iiko38/sleeperplan/published/first-model-2400x1400-options/3-courses/workshop.pdf

Sleeperplan | 9d70b40ac2ba | DRAFT_MARK_OUT_ONLY | 1

# SLEEPERPLAN / WORKSHOP PACK

### DRAFT_MARK_OUT_ONLY

## First rectangular bed draft - 2400 x 1400

As of 2026-09-06 | Generator 0.4.0 | Plan 9d70b40ac2ba3151
Worked example unless your own surveyed job file has been used. A reviewed status records human checks; it is not structural certification.
BED | OUTSIDE L x W x H (mm) | COURSES | CLEAR OPENING (mm) | FILL (litres)
first-bed-01 | 2400 x 1400 x 600 | 3 | 2200 x 1200 | 1452.0

### 12 labelled pieces | 56 fixing entries | 12 purchased sleepers | 6 saw cuts

Timber + screw purchases: GBP 354.60
Known subtotal: GBP 354.60. NOT a completed job cost. Unpriced items remain.
Cutting: exact. All explored cutting patterns and inventory states solved.
Use BUILD.md for the assembly sequence. Use cuts.csv for saw bands and fixings.csv for full coordinates. Treat all pilot entries marked UNCONFIRMED as mark-out only, not a drilling instruction.

# REVIEW GATES & ASSUMPTIONS

TYPE | CHECK
BLOCKER | Measure actual stock length/section, usable ends and saw kerf; update inputs before cutting.
BLOCKER | Review foundations, drainage, soil loads, support/bracing and any buried services on site.
BLOCKER | Review screw suitability, end-grain connections, penetration and spacing with a competent builder / supplier.
BLOCKER | Record reviewer, reviewed_on and review notes before releasing a workshop pack.
BLOCKER | Release readiness requires review.approved_physical_design_hash to equal the current physical design hash, so an edited job cannot inherit an old review. Run a draft plan, then copy the printed physical design hash into the job's review block after a genuine physical review.
NOTE | Screw heads, bearing seats, recesses and driver access are NOT modelled. On stacked courses a protruding head can stop the next course sitting flat even though all shafts pass the collision check, and recessing a seat deepens the hole and moves the tip. Confirm the head-seat detail with the actual hardware before stacking any course.
BLOCKER | wickes-287686: fixing centres are mark-out only. Confirm pilot diameter/depth or a manufacturer-supported no-pilot instruction; none is inferred.
BLOCKER | wickes-287688: fixing centres are mark-out only. Confirm pilot diameter/depth or a manufacturer-supported no-pilot instruction; none is inferred.
NOTE | first-bed-01: same corner arrangement on every course. Deliberately not interlocked; review the connection.
NOTE | first-bed-01: centre reach is approximately 700 mm from 2 accessible side(s); confirm with the user. 650 mm is a planning prompt, not an accessibility standard.
NOTE | Zero end trim assumes square, sound, usable factory/cut ends. Nominal 2400 mm is not a measurement.
NOTE | Known subtotal only; unpriced: consumables, fill, liner, preservative, site_preparation, supports, transport, labour
NOTE | Catalogue prices are dated snapshots. The configured store and collection stock are NOT confirmed.
NOTE | Geometry and straight screw-path clearance are checked; timber strength, screw capacity, long-term movement and soil pressure are NOT calculated. Supports/bracing, liner detailing and foundations are site-specific and not drawn by v1.

# PURCHASES & COSTS

Catalogue retail purchase prices as displayed; VAT is not recalculated. Explicit extras and labour are added on the same user-supplied basis. Not a tax invoice.

ITEM | NEED / BUY | LINE TOTAL
wickes-256948 - 1800 mm sleeper / matching section | 6 needed / 6 sleeper | GBP 144.00
wickes-276785 - 2400 mm sleeper / matching section | 6 needed / 6 sleeper | GBP 168.00
wickes-287686 - 7 x 150 mm screws; 25/pack | 24 needed / 2 pack | GBP 18.00
wickes-287688 - 7 x 250 mm screws; 25/pack | 32 needed / 2 pack | GBP 24.60
consumables - Drill bits, blades, PPE and other consumables | 1 needed / 1 job | UNPRICED
fill - Soil / compost / mulch supply | 1 needed / 1 job | UNPRICED
liner - Liner / protection and attachment (or explicitly not required) | 1 needed / 1 job | UNPRICED
preservative - Compatible cut-end preservative | 1 needed / 1 job | UNPRICED
site_preparation - Ground preparation / bedding / disposal | 1 needed / 1 job | UNPRICED
supports - Site-specific stakes, bracing, brackets and their fixings | 1 needed / 1 job | UNPRICED
transport - Collection / delivery / travel | 1 needed / 1 job | UNPRICED
labour - Labour (nearest penny, half-up) | UNCONFIRMED | UNPRICED

### Known subtotal: GBP 354.60

## Parts and fixings board / visual checklist (page 1 of 2)

DRAFT_MARK_OUT_ONLY | Verify quantity and ID before each step

TOOLS / HANDLING

[2x] two people for long/heavy members
[CHECK] confirm A/TOP/OUTER labels [STOP] resolve blockers before drilling Hammer + driver/bit set + square/level

FASTENERS

wickes-287686

7 x 150 mm
Need 24 entries

Pilot UNCONFIRMED

wickes-287688

7 x 250 mm
Need 32 entries

Pilot UNCONFIRMED

TIMBER PARTS

PIECE ID | BED | COURSE | SIDE | LENGTH | SECTION | BOARD | A DATUM
first-bed-01-C1-E first-bed-01 | 1 | E | 1200 | 100x200 | B007 | Lower X/Y end
first-bed-01-C1-N first-bed-01 | 1 | N | 2400 | 100x200 | B001 | Lower X/Y end
first-bed-01-C1-S first-bed-01 | 1 | S | 2400 | 100x200 | B002 | Lower X/Y end
first-bed-01-C1-W first-bed-01 | 1 | W | 1200 | 100x200 | B008 | Lower X/Y end
first-bed-01-C2-E first-bed-01 | 2 | E | 1200 | 100x200 | B009 | Lower X/Y end
first-bed-01-C2-N first-bed-01 | 2 | N | 2400 | 100x200 | B003 | Lower X/Y end
first-bed-01-C2-S first-bed-01 | 2 | S | 2400 | 100x200 | B004 | Lower X/Y end
first-bed-01-C2-W first-bed-01 | 2 | W | 1200 | 100x200 | B010 | Lower X/Y end
first-bed-01-C3-E first-bed-01 | 3 | E | 1200 | 100x200 | B011 | Lower X/Y end
first-bed-01-C3-N first-bed-01 | 3 | N | 2400 | 100x200 | B005 | Lower X/Y end

Use this board as the pre-flight checklist. Exact cut order and coordinates remain in cuts.csv and fixings.csv.

# Parts and fixings board / visual checklist (page 2 of 2)

DRAFT_MARK_OUT_ONLY | Verify quantity and ID before each step
TIMBER PARTS (continued)
PIECE ID | BED | COURSE | SIDE | LENGTH | SECTION | BOARD | A DATUM
first-bed-01-C3-S first-bed-01 | 3 | S | 2400 | 100x200 | B006 | Lower X/Y end
first-bed-01-C3-W first-bed-01 | 3 | W | 1200 | 100x200 | B012 | Lower X/Y end

Use this board as the pre-flight checklist. Exact cut order and coordinates remain in cuts.csv and fixings.csv.

# Workshop process / script-driven sequence

DRAFT_MARK_OUT_ONLY | Follow these steps with BUILD.md, cuts.csv and fixings.csv
1. Receive and inspect timber stock; reject twisted/split members.
2. Label each stock board Bxx and mark datum A before any cut.
3. Execute cuts.csv in sequence; kerf_start..kerf_end is waste band.
4. Re-label produced parts and preserve A / TOP / OUTER orientation.
5. Drill and drive by piece fixing sheets (exact U, V, W coordinates).
6. Assemble course-by-course using per-course plan sheets.

CORRECT

Check entry face, direction arrow and quantity before each action.

INCORRECT

Never drill or drive when pilot_mode is UNCONFIRMED.

All positions, lengths and hardware IDs are generated from plan geometry; do not freehand from screenshots.

# Stock arrival, board IDs and datum A (page 1 of 2)

Label before cutting; keep original A datum for every stock item

B001 | wickes-276785 | gross 2400 mm

A

2400 mm
B002 | wickes-276785 | gross 2400 mm

A

2400 mm
B003 | wickes-276785 | gross 2400 mm

A

2400 mm
B004 | wickes-276785 | gross 2400 mm

A

2400 mm
B005 | wickes-276785 | gross 2400 mm

A

2400 mm
B006 | wickes-276785 | gross 2400 mm

A

2400 mm
B007 | wickes-256948 | gross 1800 mm

A

1800 mm
B008 | wickes-256948 | gross 1800 mm

A

1800 mm

Use these B IDs in parts.csv and cuts.csv. Datum A in cut coordinates always refers to original stock, not the finished part.

# Stock arrival, board IDs and datum A (page 2 of 2)

Label before cutting; keep original A datum for every stock item

B009 | wickes-256948 | gross 1800 mm

A

1800 mm
B010 | wickes-256948 | gross 1800 mm

A

1800 mm
B011 | wickes-256948 | gross 1800 mm

A

1800 mm
B012 | wickes-256948 | gross 1800 mm

A

1800 mm

Use these B IDs in parts.csv and cuts.csv. Datum A in cut coordinates always refers to original stock, not the finished part.

# Fastener card / wickes-287686

Use with piece fixing sheets for exact side and coordinates

Cross-section view (not to scale in thickness)

through member 100 mm | receiver penetration 50 mm

screw 7 x 150 mm

150 mm nominal Used in fixing kinds: corner

Entry faces in this plan: outer
Entries scheduled: 24

Pilot: UNCONFIRMED - stop and confirm drill bit diameter/depth before drilling.

Exact side, point and direction are in piece fixing sheets and fixings.csv (U from A, V, W, and direction XYZ).

# Fastener card / wickes-287688

Use with piece fixing sheets for exact side and coordinates

Cross-section view (not to scale in thickness)

through member 200 mm | receiver penetration 50 mm

screw 7 x 250 mm

250 mm nominal Used in fixing kinds: stack

Entry faces in this plan: top
Entries scheduled: 32

Pilot: UNCONFIRMED - stop and confirm drill bit diameter/depth before drilling.

Exact side, point and direction are in piece fixing sheets and fixings.csv (U from A, V, W, and direction XYZ).

# first-bed-01 / 3 courses / assembled view

DRAFT_MARK_OUT_ONLY | Same timber section throughout | Schematic colour, not a finish sample


## Outside: 2400 x 1400 x 600 mm | Clear opening: 2200 x 1200 mm

Geometric fill: 1452 litres at 50 mm below the top. No settlement allowance.

# first-bed-01 / course 1 / plan view

DRAFT_MARK_OUT_ONLY | All dimensions mm | Origin O = outside S/W corner | NOT a 1:1 template

### Outside 2400

Outside 1400

Clear opening 2200 x 1200

### Outside diagonals: 2778.5 mm (both equal)

O S / +X runs left to right; +Y runs towards N

Circles = top fixing entries. Arrows = two corner screws at different heights.
Piece sheets give the entry face, datum, coordinates and hardware. A is each piece's lower-X / lower-Y end.

# first-bed-01 / course 2 / plan view

DRAFT_MARK_OUT_ONLY | All dimensions mm | Origin O = outside S/W corner | NOT a 1:1 template

### Outside 2400

Outside 1400

Clear opening 2200 x 1200

### Outside diagonals: 2778.5 mm (both equal)

O S / +X runs left to right; +Y runs towards N

Circles = top fixing entries. Arrows = two corner screws at different heights.
Piece sheets give the entry face, datum, coordinates and hardware. A is each piece's lower-X / lower-Y end.

# first-bed-01 / course 3 / plan view

DRAFT_MARK_OUT_ONLY | All dimensions mm | Origin O = outside S/W corner | NOT a 1:1 template

### Outside 2400

Outside 1400

Clear opening 2200 x 1200

### Outside diagonals: 2778.5 mm (both equal)

O S / +X runs left to right; +Y runs towards N

Circles = top fixing entries. Arrows = two corner screws at different heights.
Piece sheets give the entry face, datum, coordinates and hardware. A is each piece's lower-X / lower-Y end.

# Stock allocation / cutting diagram

Measure every kerf band from ORIGINAL stock datum A. Finished pieces are exact; this drawing is NOT to scale for tracing.

### B001 | wickes-276785 | 2400 mm | 0 saw cuts | offcut 0 mm

first-bed-01-C1-N

2400

A

Waste kerf bands from original A (mm): none - use the sound full length

### B002 | wickes-276785 | 2400 mm | 0 saw cuts | offcut 0 mm

first-bed-01-C1-S

2400

A

Waste kerf bands from original A (mm): none - use the sound full length

### B003 | wickes-276785 | 2400 mm | 0 saw cuts | offcut 0 mm

first-bed-01-C2-N

2400

A

Waste kerf bands from original A (mm): none - use the sound full length

### B004 | wickes-276785 | 2400 mm | 0 saw cuts | offcut 0 mm

first-bed-01-C2-S

2400

A

Waste kerf bands from original A (mm): none - use the sound full length

### B005 | wickes-276785 | 2400 mm | 0 saw cuts | offcut 0 mm

first-bed-01-C3-N

2400

A

Waste kerf bands from original A (mm): none - use the sound full length

Exact saw band positions and blade-centre coordinates are in cuts.csv. Kerf widths here may be exaggerated for visibility.

# Stock allocation / cutting diagram

Measure every kerf band from ORIGINAL stock datum A. Finished pieces are exact; this drawing is NOT to scale for tracing.

### B006 | wickes-276785 | 2400 mm | 0 saw cuts | offcut 0 mm

first-bed-01-C3-S

2400

A

Waste kerf bands from original A (mm): none - use the sound full length

### B007 | wickes-256948 | 1800 mm | 1 saw cuts | offcut 597 mm

first-bed-01-C1-E

1200

A

Waste kerf bands from original A (mm): 1200..1203

### B008 | wickes-256948 | 1800 mm | 1 saw cuts | offcut 597 mm

first-bed-01-C1-W

1200

A

Waste kerf bands from original A (mm): 1200..1203

### B009 | wickes-256948 | 1800 mm | 1 saw cuts | offcut 597 mm

first-bed-01-C2-E

1200

A

Waste kerf bands from original A (mm): 1200..1203

### B010 | wickes-256948 | 1800 mm | 1 saw cuts | offcut 597 mm

first-bed-01-C2-W

1200

A

Waste kerf bands from original A (mm): 1200..1203

Exact saw band positions and blade-centre coordinates are in cuts.csv. Kerf widths here may be exaggerated for visibility.

# Stock allocation / cutting diagram

Measure every kerf band from ORIGINAL stock datum A. Finished pieces are exact; this drawing is NOT to scale for tracing.

### B011 | wickes-256948 | 1800 mm | 1 saw cuts | offcut 597 mm

first-bed-01-C3-E

1200

A

Waste kerf bands from original A (mm): 1200..1203

### B012 | wickes-256948 | 1800 mm | 1 saw cuts | offcut 597 mm

first-bed-01-C3-W

1200

A

Waste kerf bands from original A (mm): 1200..1203

Exact saw band positions and blade-centre coordinates are in cuts.csv. Kerf widths here may be exaggerated for visibility.

# first-bed-01-C1-S / 2400 x 100 x 200 mm

V=0 edge; corner x1; outer

DRAFT_MARK_OUT_ONLY | Datum A = lower global X end | Coordinates in mm, rounded to 0.1 for display

TOP FACE / U along length; V across width from its lower-coordinate edge

A

OUTER FACE / U from A; W measured UP from bottom / side S

A

Views intentionally stretch section depth for legibility. Use the coordinates below, not a ruler on this sheet.

FIXING | FACE | U FROM A | V | W UP | SCREW | PILOT
F01 | outer | 50 | 0 | 50 | 7 x 150 | UNCONFIRMED - mark out only
F02 | outer | 50 | 0 | 150 | 7 x 150 | UNCONFIRMED - mark out only
F03 | outer | 2350 | 0 | 50 | 7 x 150 | UNCONFIRMED - mark out only
F04 | outer | 2350 | 0 | 150 | 7 x 150 | UNCONFIRMED - mark out only

# first-bed-01-C1-N / 2400 x 100 x 200 mm

V=0 edge; corner x1; outer

DRAFT_MARK_OUT_ONLY | Datum A = lower global X end | Coordinates in mm, rounded to 0.1 for display

TOP FACE / U along length; V across width from its lower-coordinate edge

A

OUTER FACE / U from A; W measured UP from bottom / side N

A

Views intentionally stretch section depth for legibility. Use the coordinates below, not a ruler on this sheet.

FIXING | FACE | U FROM A | V | W UP | SCREW | PILOT
F01 | outer | 50 | 100 | 50 | 7 x 150 | UNCONFIRMED - mark out only
F02 | outer | 50 | 100 | 150 | 7 x 150 | UNCONFIRMED - mark out only
F03 | outer | 2350 | 100 | 50 | 7 x 150 | UNCONFIRMED - mark out only
F04 | outer | 2350 | 100 | 150 | 7 x 150 | UNCONFIRMED - mark out only

# first-bed-01-C1-W / 1200 x 100 x 200 mm

DRAFT_MARK_OUT_ONLY | Datum A = lower global Y end | Coordinates in mm, rounded to 0.1 for display

TOP FACE / U along length; V across width from its lower-coordinate edge

A

V=0 edge
OUTER FACE / U from A; W measured UP from bottom / side W

A

Views intentionally stretch section depth for legibility. Use the coordinates below, not a ruler on this sheet.

FIXING | FACE | U FROM A | V | W UP | SCREW | PILOT

No screw entry points on this piece; it receives screws from adjoining members.

# first-bed-01-C1-E / 1200 x 100 x 200 mm

DRAFT_MARK_OUT_ONLY | Datum A = lower global Y end | Coordinates in mm, rounded to 0.1 for display

TOP FACE / U along length; V across width from its lower-coordinate edge

A

V=0 edge
OUTER FACE / U from A; W measured UP from bottom / side E

A

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

FIXING | FACE | U FROM A | V | W UP | SCREW | PILOT

No screw entry points on this piece; it receives screws from adjoining members.

# first-bed-01-C2-S / 2400 x 100 x 200 mm

V=0 edge; corner x1; outer; stack x1; top; vertical

DRAFT_MARK_OUT_ONLY | Datum A = lower global X end | Coordinates in mm, rounded to 0.1 for display

TOP FACE / U along length; V across width from its lower-coordinate edge

A

OUTER FACE / U from A; W measured UP from bottom / side S

A

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

FIXING | FACE | U FROM A | V | W UP | SCREW | PILOT
F01 | outer | 50 | 0 | 50 | 7 x 150 | UNCONFIRMED - mark out only
F02 | outer | 50 | 0 | 150 | 7 x 150 | UNCONFIRMED - mark out only
F03 | outer | 2350 | 0 | 50 | 7 x 150 | UNCONFIRMED - mark out only
F04 | outer | 2350 | 0 | 150 | 7 x 150 | UNCONFIRMED - mark out only
F05 | top | 200 | 50 | 200 | 7 x 250 | UNCONFIRMED - mark out only
F06 | top | 700 | 50 | 200 | 7 x 250 | UNCONFIRMED - mark out only
F07 | top | 1200 | 50 | 200 | 7 x 250 | UNCONFIRMED - mark out only
F08 | top | 1700 | 50 | 200 | 7 x 250 | UNCONFIRMED - mark out only
F09 | top | 2200 | 50 | 200 | 7 x 250 | UNCONFIRMED - mark out only

# first-bed-01-C2-N / 2400 x 100 x 200 mm

V=0 edge; corner x1; outer; stack x1; top; vertical

DRAFT_MARK_OUT_ONLY | Datum A = lower global X end | Coordinates in mm, rounded to 0.1 for display

TOP FACE / U along length; V across width from its lower-coordinate edge

A

OUTER FACE / U from A; W measured UP from bottom / side N

A

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

FIXING | FACE | U FROM A | V | W UP | SCREW | PILOT
F01 | outer | 50 | 100 | 50 | 7 x 150 | UNCONFIRMED - mark out only
F02 | outer | 50 | 100 | 150 | 7 x 150 | UNCONFIRMED - mark out only
F03 | outer | 2350 | 100 | 50 | 7 x 150 | UNCONFIRMED - mark out only
F04 | outer | 2350 | 100 | 150 | 7 x 150 | UNCONFIRMED - mark out only
F05 | top | 200 | 50 | 200 | 7 x 250 | UNCONFIRMED - mark out only
F06 | top | 700 | 50 | 200 | 7 x 250 | UNCONFIRMED - mark out only
F07 | top | 1200 | 50 | 200 | 7 x 250 | UNCONFIRMED - mark out only
F08 | top | 1700 | 50 | 200 | 7 x 250 | UNCONFIRMED - mark out only
F09 | top | 2200 | 50 | 200 | 7 x 250 | UNCONFIRMED - mark out only

# first-bed-01-C2-W / 1200 x 100 x 200 mm

V=0 edge; stack x1; top; vertical

DRAFT_MARK_OUT_ONLY | Datum A = lower global Y end | Coordinates in mm, rounded to 0.1 for display

TOP FACE / U along length; V across width from its lower-coordinate edge

A

OUTER FACE / U from A; W measured UP from bottom / side W

A

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

FIXING | FACE | U FROM A | V | W UP | SCREW | PILOT
F01 | top | 200 | 50 | 200 | 7 x 250 | UNCONFIRMED - mark out only
F02 | top | 600 | 50 | 200 | 7 x 250 | UNCONFIRMED - mark out only
F03 | top | 1000 | 50 | 200 | 7 x 250 | UNCONFIRMED - mark out only

# first-bed-01-C2-E / 1200 x 100 x 200 mm

DRAFT_MARK_OUT_ONLY | Datum A = lower global Y end | Coordinates in mm, rounded to 0.1 for display

TOP FACE / U along length; V across width from its lower-coordinate edge

A

OUTER FACE / U from A; W measured UP from bottom / side E

A

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

FIXING | FACE | U FROM A | V | W UP | SCREW | PILOT
F01 | top | 200 | 50 | 200 | 7 x 250 | UNCONFIRMED - mark out only
F02 | top | 600 | 50 | 200 | 7 x 250 | UNCONFIRMED - mark out only
F03 | top | 1000 | 50 | 200 | 7 x 250 | UNCONFIRMED - mark out only

# first-bed-01-C3-S / 2400 x 100 x 200 mm

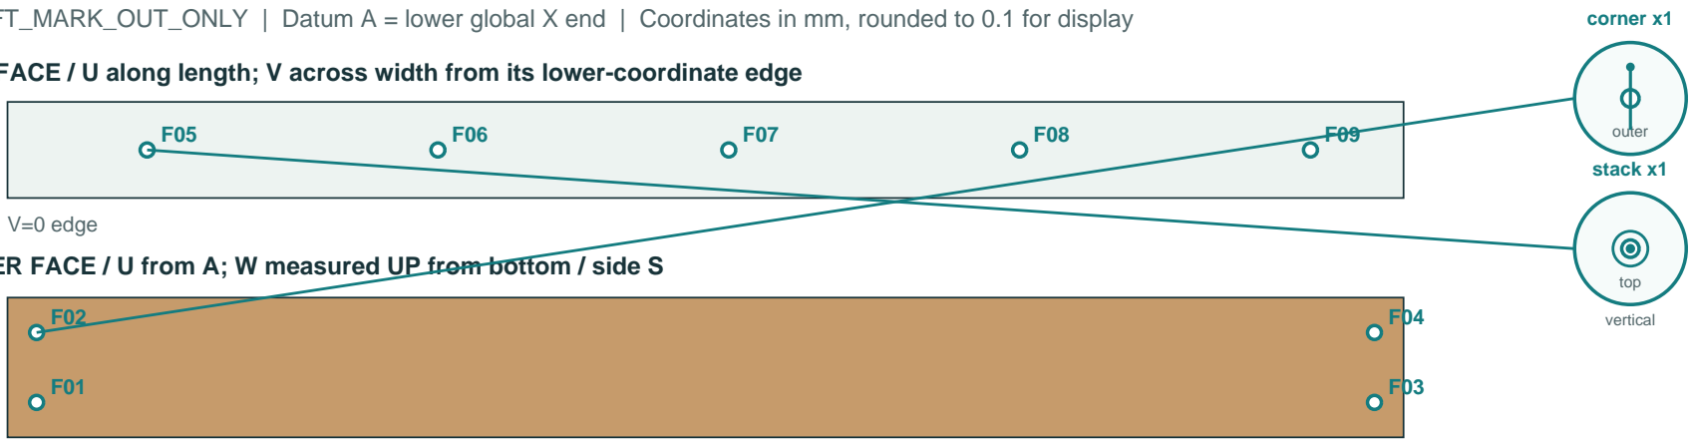
[picture p18: figure]
V=0 edge; corner x1; outer; stack x1; top; vertical

DRAFT_MARK_OUT_ONLY | Datum A = lower global X end | Coordinates in mm, rounded to 0.1 for display

TOP FACE / U along length; V across width from its lower-coordinate edge

A

OUTER FACE / U from A; W measured UP from bottom / side S

A

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

FIXING | FACE | U FROM A | V | W UP | SCREW | PILOT
F01 | outer | 50 | 0 | 50 | 7 x 150 | UNCONFIRMED - mark out only
F02 | outer | 50 | 0 | 150 | 7 x 150 | UNCONFIRMED - mark out only
F03 | outer | 2350 | 0 | 50 | 7 x 150 | UNCONFIRMED - mark out only
F04 | outer | 2350 | 0 | 150 | 7 x 150 | UNCONFIRMED - mark out only
F05 | top | 240 | 50 | 200 | 7 x 250 | UNCONFIRMED - mark out only
F06 | top | 740 | 50 | 200 | 7 x 250 | UNCONFIRMED - mark out only
F07 | top | 1240 | 50 | 200 | 7 x 250 | UNCONFIRMED - mark out only
F08 | top | 1740 | 50 | 200 | 7 x 250 | UNCONFIRMED - mark out only
F09 | top | 2240 | 50 | 200 | 7 x 250 | UNCONFIRMED - mark out only

# first-bed-01-C3-N / 2400 x 100 x 200 mm

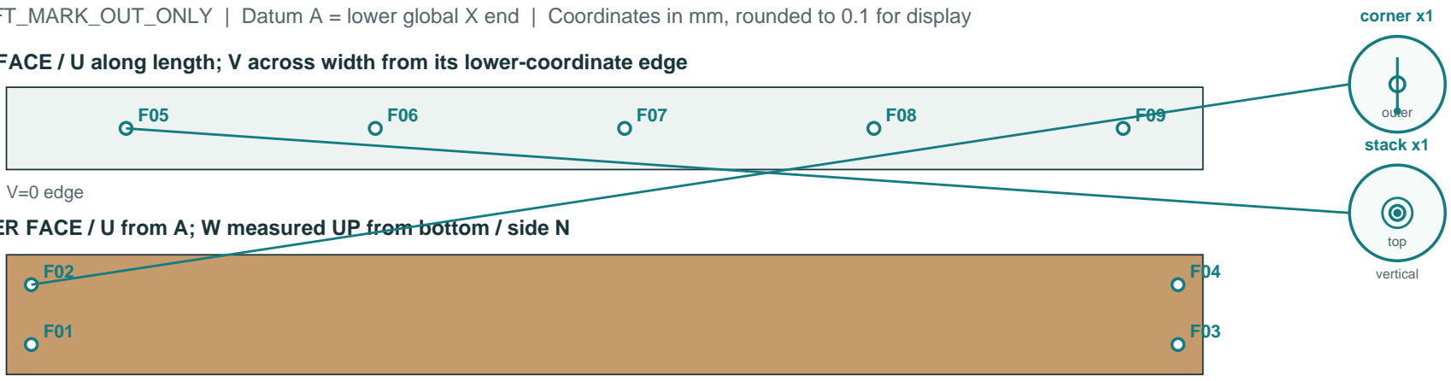
[picture p19: figure]
V=0 edge; corner x1; outer; stack x1; top; vertical

DRAFT_MARK_OUT_ONLY | Datum A = lower global X end | Coordinates in mm, rounded to 0.1 for display

TOP FACE / U along length; V across width from its lower-coordinate edge

A

OUTER FACE / U from A; W measured UP from bottom / side N

A

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

FIXING | FACE | U FROM A | V | W UP | SCREW | PILOT
F01 | outer | 50 | 100 | 50 | 7 x 150 | UNCONFIRMED - mark out only
F02 | outer | 50 | 100 | 150 | 7 x 150 | UNCONFIRMED - mark out only
F03 | outer | 2350 | 100 | 50 | 7 x 150 | UNCONFIRMED - mark out only
F04 | outer | 2350 | 100 | 150 | 7 x 150 | UNCONFIRMED - mark out only
F05 | top | 240 | 50 | 200 | 7 x 250 | UNCONFIRMED - mark out only
F06 | top | 740 | 50 | 200 | 7 x 250 | UNCONFIRMED - mark out only
F07 | top | 1240 | 50 | 200 | 7 x 250 | UNCONFIRMED - mark out only
F08 | top | 1740 | 50 | 200 | 7 x 250 | UNCONFIRMED - mark out only
F09 | top | 2240 | 50 | 200 | 7 x 250 | UNCONFIRMED - mark out only

# first-bed-01-C3-W / 1200 x 100 x 200 mm

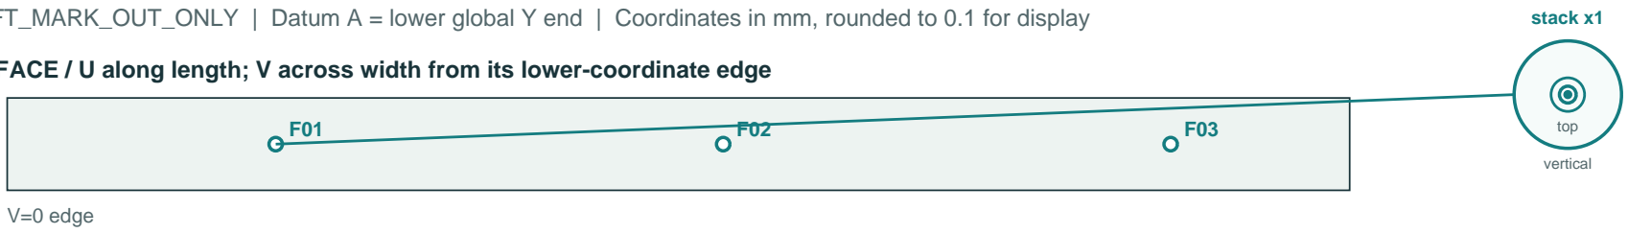
[picture p20: figure]
V=0 edge; stack x1; top; vertical

DRAFT_MARK_OUT_ONLY | Datum A = lower global Y end | Coordinates in mm, rounded to 0.1 for display

TOP FACE / U along length; V across width from its lower-coordinate edge

A

OUTER FACE / U from A; W measured UP from bottom / side W

A

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

FIXING | FACE | U FROM A | V | W UP | SCREW | PILOT
F01 | top | 240 | 50 | 200 | 7 x 250 | UNCONFIRMED - mark out only
F02 | top | 640 | 50 | 200 | 7 x 250 | UNCONFIRMED - mark out only
F03 | top | 1040 | 50 | 200 | 7 x 250 | UNCONFIRMED - mark out only

# first-bed-01-C3-E / 1200 x 100 x 200 mm

DRAFT_MARK_OUT_ONLY | Datum A = lower global Y end | Coordinates in mm, rounded to 0.1 for display

TOP FACE / U along length; V across width from its lower-coordinate edge

A

OUTER FACE / U from A; W measured UP from bottom / side E

A

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

FIXING | FACE | U FROM A | V | W UP | SCREW | PILOT
F01 | top | 240 | 50 | 200 | 7 x 250 | UNCONFIRMED - mark out only
F02 | top | 640 | 50 | 200 | 7 x 250 | UNCONFIRMED - mark out only
F03 | top | 1040 | 50 | 200 | 7 x 250 | UNCONFIRMED - mark out only
